TeraVolt-Labs/USB-TTL-Converter/Images/USB_TTL_2025-Jun-29_11-45-25AM-000_CustomizedView4288134034 Background Removed.png

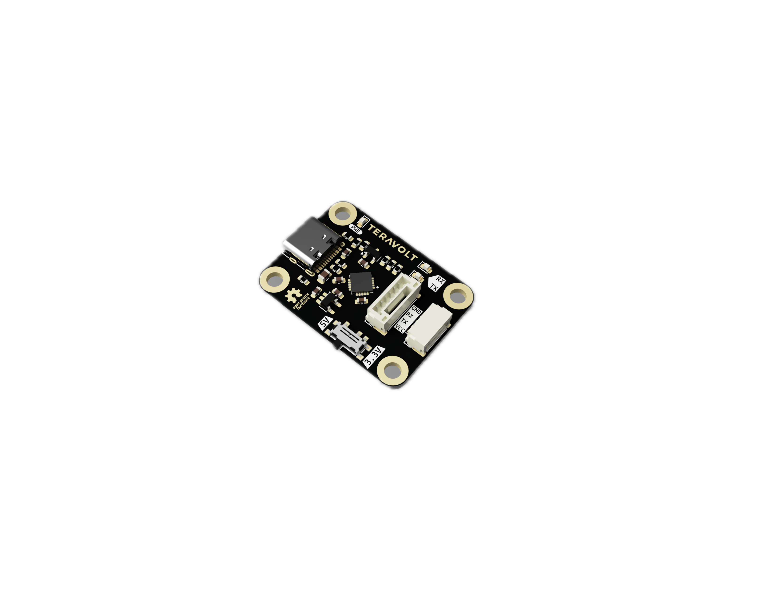
Images/USB_TTL_2025-Jun-29_11-45-25AM-000_CustomizedView4288134034 Background Removed.png
